dekkit/RGB-to-Component-Transcoder/VA02a/PCB_PCB_2020-04-10 17_26_57_2020-06-04_12-55-12.png

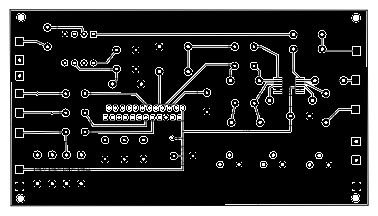
VA02a/PCB_PCB_2020-04-10 17_26_57_2020-06-04_12-55-12.png
