dekkit/RGB-to-Component-Transcoder/VA01/RGB2Component_Dek_PCB_Visual_v1.00.png

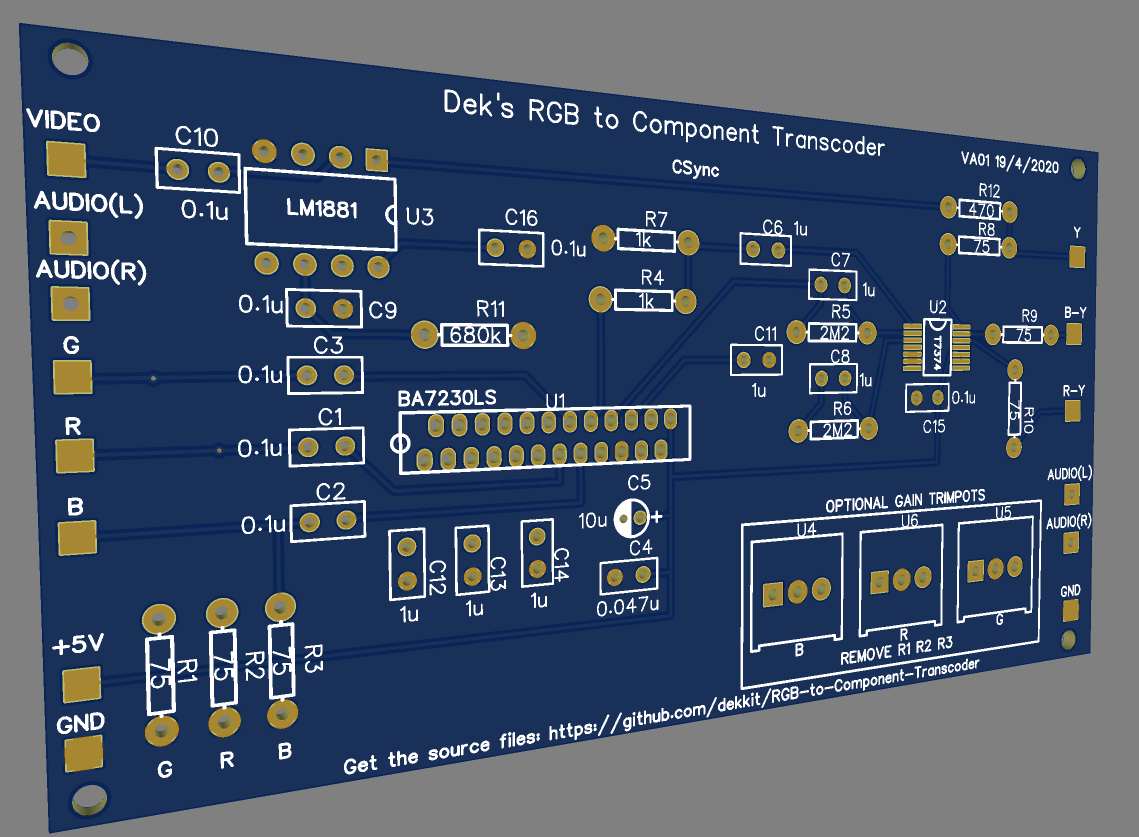
VA01/RGB2Component_Dek_PCB_Visual_v1.00.png
