dekkit/RGB-to-Component-Transcoder/VA02/Schematic_RGB to Component Transcoder_2020-05-17_21-51-17.png

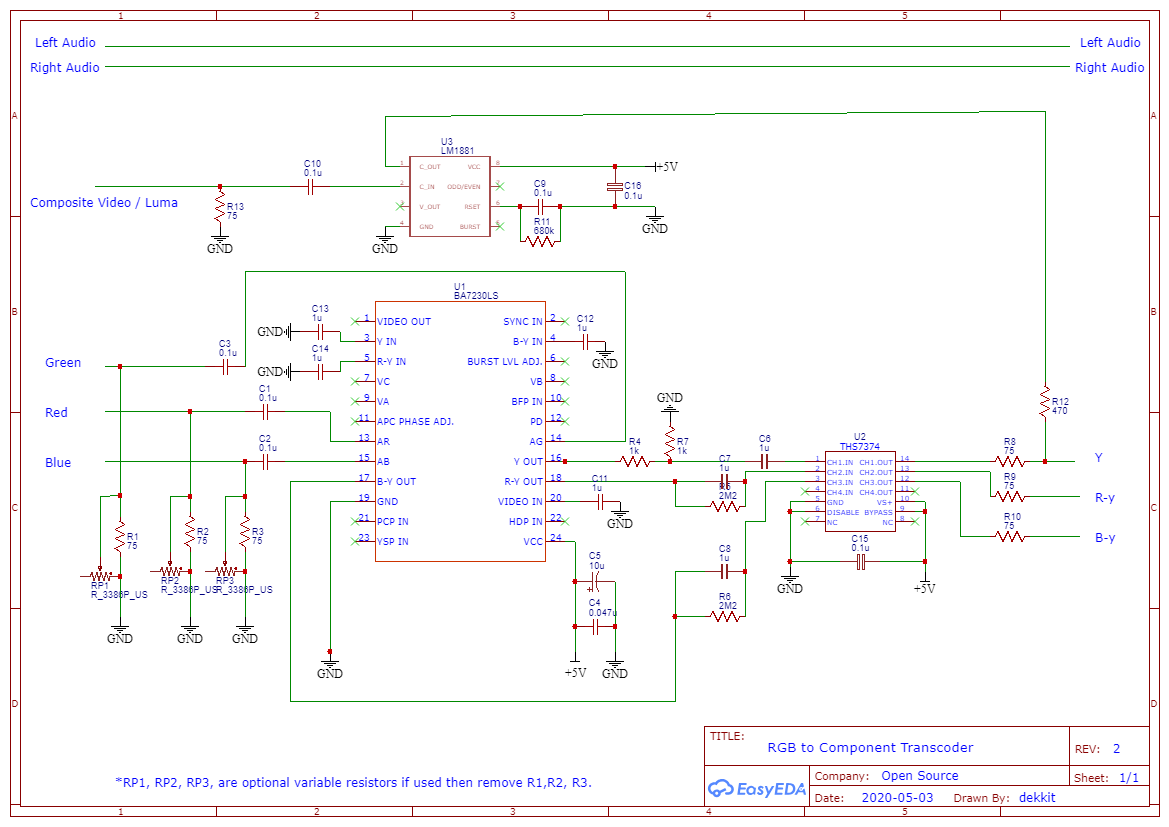
VA02/Schematic_RGB to Component Transcoder_2020-05-17_21-51-17.png
