dekkit/RGB-to-Component-Transcoder/Test Results/Initial Scope Test (VA02a Schematic)/lm1881_sync_out_before_R12.png

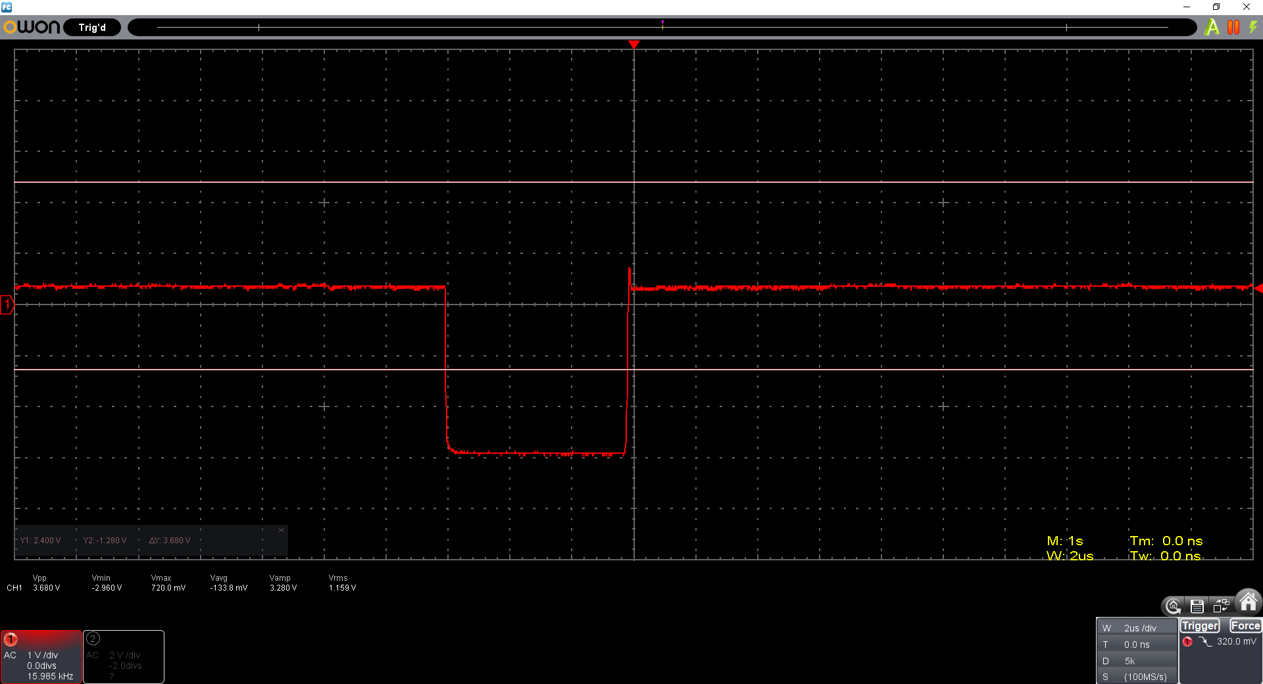
Test Results/Initial Scope Test (VA02a Schematic)/lm1881_sync_out_before_R12.png
