dekkit/RGB-to-Component-Transcoder/Test Results/Initial Scope Test (VA02a Schematic)/Y(GREEN)_out_pp.png

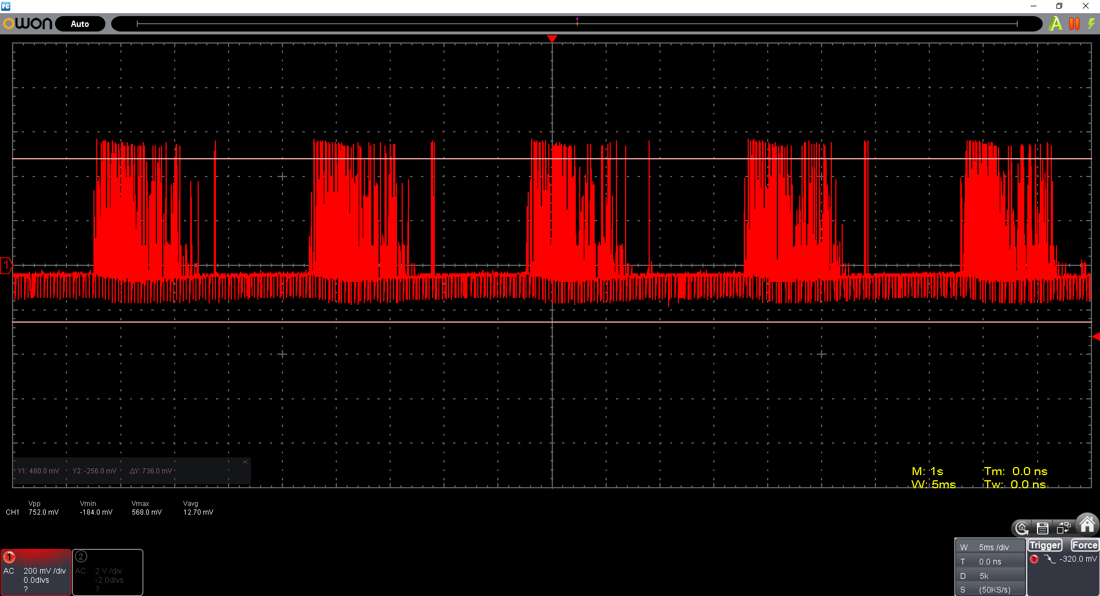
Test Results/Initial Scope Test (VA02a Schematic)/Y(GREEN)_out_pp.png
