dekkit/RGB-to-Component-Transcoder/Test Results/Initial Scope Test (VA02a Schematic)/Y-b(BLUE)_out_pp.png

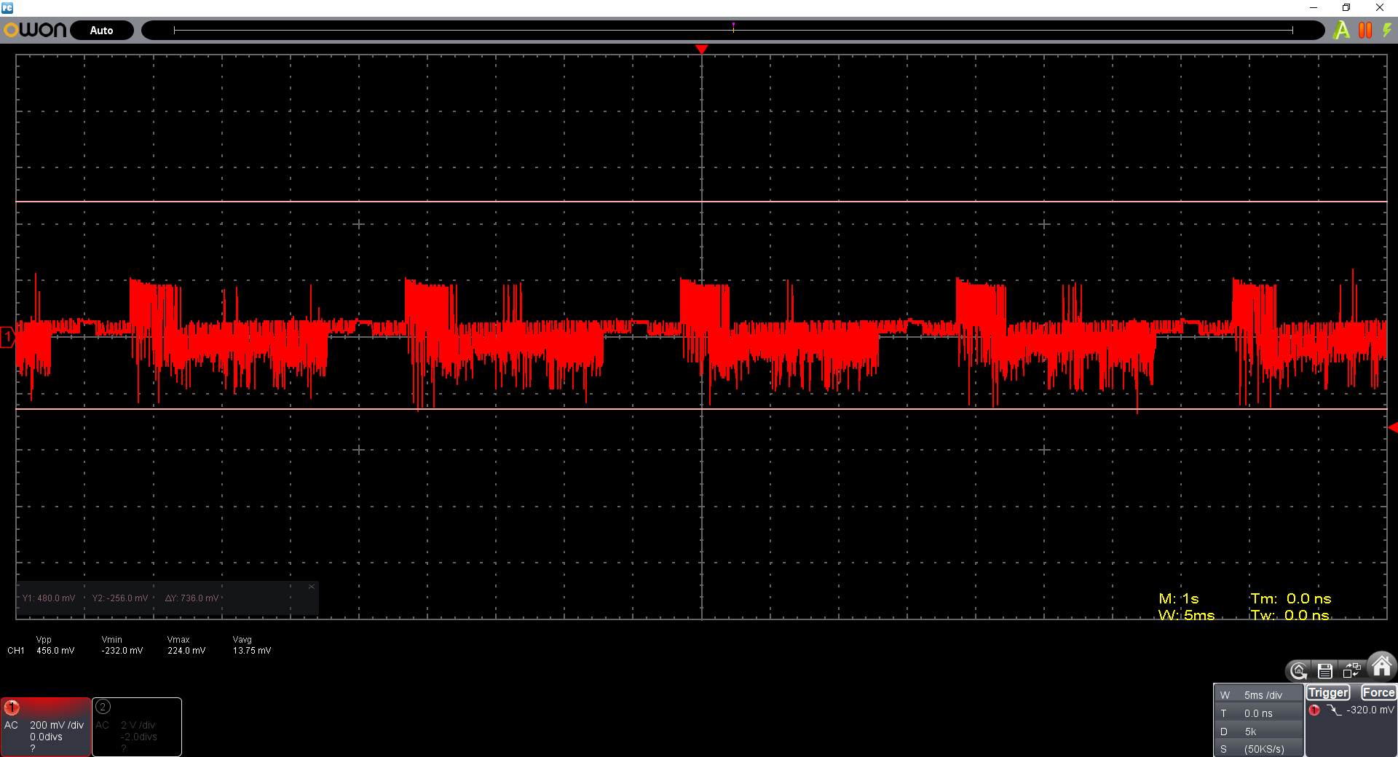
Test Results/Initial Scope Test (VA02a Schematic)/Y-b(BLUE)_out_pp.png
