dekkit/RGB-to-Component-Transcoder/Test Results/Power Interference Test (USB and HDD)/hdd2.png

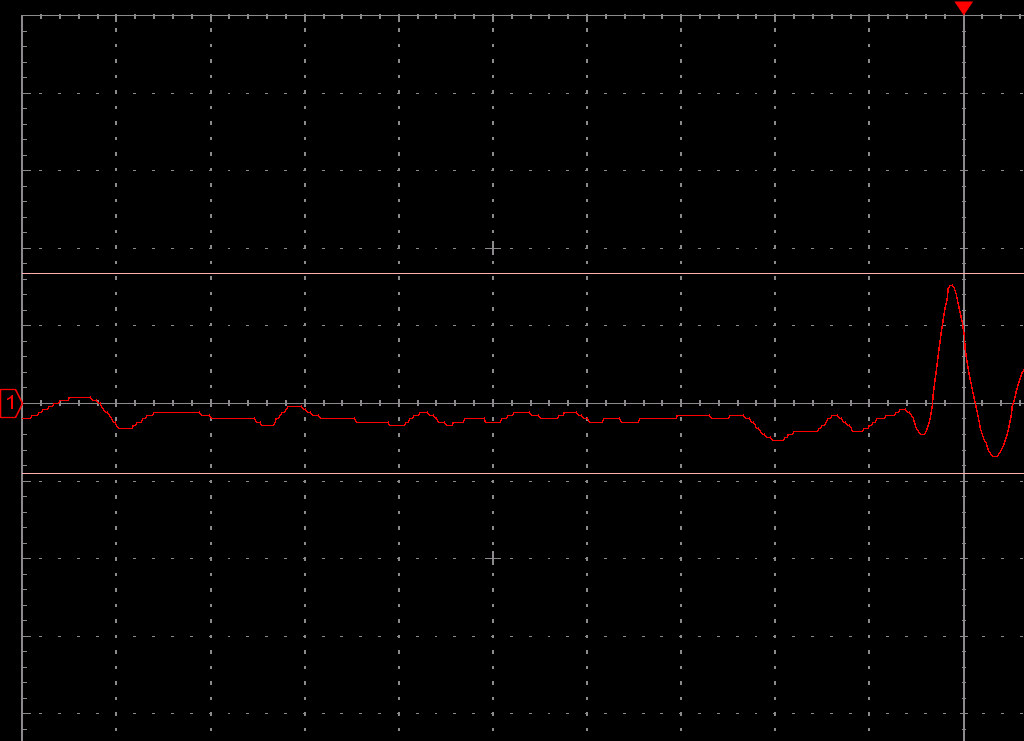
Test Results/Power Interference Test (USB and HDD)/hdd2.png
